himalayanelixir/arduino-pi-ceiling-sculpture/parts/pcbs/motor-top.png

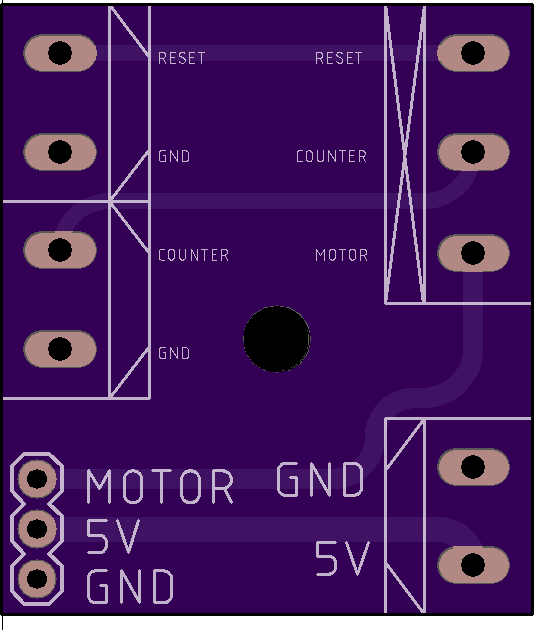
parts/pcbs/motor-top.png
