himalayanelixir/arduino-pi-ceiling-sculpture/rodincom/rodincom.ino

#include <Wire.h>
#include <Adafruit_PWMServoDriver.h>
#include <String.h> 

Adafruit_PWMServoDriver pwm = Adafruit_PWMServoDriver();

#define SERVOSPEED  150

const byte numChars = 32;
char receivedChars[numChars];

boolean newData = false;

int m1_sensor_pin = A0;  
int m1_sensor_value1 = 0;
int m1_sensor_value2 = 0;

void setup() {
    Serial.begin(9600);
    Serial.println("<Arduino is ready>");

    pwm.begin();
    pwm.setPWMFreq(50);
    delay(10);
    pwm.setPWM(3, 0, 0);
}

void loop() {
    recvWithStartEndMarkers();
    showNewData();
}

void recvWithStartEndMarkers() {
    static boolean recvInProgress = false;
    static byte ndx = 0;
    char startMarker = '<';
    char endMarker = '>';
    char rc;
 
    while (Serial.available() > 0 && newData == false) {
        rc = Serial.read();

        if (recvInProgress == true) {
            if (rc != endMarker) {
                receivedChars[ndx] = rc;
                ndx++;
                if (ndx >= numChars) {
                    ndx = numChars - 1;
                }
            }
            else {
                receivedChars[ndx] = '\0'; // terminate the string
                recvInProgress = false;
                ndx = 0;
                newData = true;
            }
        }

        else if (rc == startMarker) {
            recvInProgress = true;
        }
    }
}

void processData() {
  String recievedString = receivedChars;
  Serial.println("<"); 
  Serial.print("RevievedString: ");
  Serial.println(recievedString);
  String m1_rotation_direction = getValue(recievedString, ',', 0);  
  String m1_rotation = getValue(recievedString, ',', 1);
  int m1_rotation_int = m1_rotation.toInt();
  Serial.print("Number of Rotations: ");
  Serial.println(m1_rotation);
  
  if (m1_rotation_direction == "Up") {
    Serial.println("<");  
    Serial.print("Arduino: ");
    Serial.println("Moving Up!");
    pwm.setPWM(3, 0, 295);
    while (1) {
      readValues();
      Serial.println(m1_sensor_value2);
      if (m1_sensor_value1 < 500 && m1_sensor_value2 > 500){
          m1_rotation_int = m1_rotation_int - 1;
      }

      if (m1_rotation_int == 0){
        break;
      }
     delay(500);
    }
   pwm.setPWM(3, 0, 0);

  }
  else if (m1_rotation_direction == "Down") {
    Serial.println("<");  
    Serial.print("Arduino: ");
    Serial.println("Moving Down!");
    pwm.setPWM(3, 0, 270);
    while (1) {
      readValues();
      Serial.println(m1_sensor_value2);
      if (m1_sensor_value1 < 500 && m1_sensor_value2 > 500){
          m1_rotation_int = m1_rotation_int - 1;
      }

      if (m1_rotation_int == 0){
        break;
      }
     delay(500);
    }
   pwm.setPWM(3, 0, 0);
  }

  else if (strcmp(receivedChars,"Stop")==0){
      Serial.println("<");  
      Serial.print("Arduino: ");
      Serial.println("Moving Stopping!");
      pwm.setPWM(3, 0, 0);
  }
  else
  {
      Serial.println("<");  
      Serial.print("Arduino: ");
      Serial.println("Invalid Input!");
  }
}
void showNewData() {
  if (newData == true) {
      processData();  
      //Serial.print("Arduino: ");
      //Serial.println(receivedChars);
      Serial.println(">");
      newData = false;
  }
}

void readValues() {
  m1_sensor_value1 = m1_sensor_value2;
  m1_sensor_value2 = analogRead(m1_sensor_pin); 
}

String getValue(String data, char separator, int index)
{
    int found = 0;
    int strIndex[] = { 0, -1 };
    int maxIndex = data.length() - 1;

    for (int i = 0; i <= maxIndex && found <= index; i++) {
        if (data.charAt(i) == separator || i == maxIndex) {
            found++;
            strIndex[0] = strIndex[1] + 1;
            strIndex[1] = (i == maxIndex) ? i+1 : i;
        }
    }
    return found > index ? data.substring(strIndex[0], strIndex[1]) : "";
}
